SSIM-RE/MotionGame/firmware/MotionGame/menu_icons.cpp

#include"menu_icons.h"

const uint8_t ICON_GAME_64[512] = {
    0x00, 0x00, 0x00, 0x00, 0x00, 0x00, 0x00, 0x00, 0x00, 0x00, 0x00, 0x00,
    0x00, 0x00, 0x00, 0x00, 0x00, 0x00, 0x00, 0x00, 0x00, 0x00, 0x00, 0x00,
    0x00, 0x00, 0x00, 0x00, 0x00, 0x00, 0x00, 0x00, 0x00, 0x00, 0x00, 0x00,
    0x00, 0x00, 0x00, 0x00, 0x00, 0x00, 0x00, 0x00, 0x00, 0x00, 0x00, 0x00,
    0x00, 0x00, 0x00, 0x00, 0x00, 0x00, 0x00, 0x00, 0x00, 0x00, 0x00, 0x00,
    0x00, 0x00, 0x00, 0x00, 0x00, 0x00, 0x00, 0x00, 0x00, 0x00, 0x00, 0x00,
    0x00, 0x00, 0x00, 0x00, 0x00, 0x00, 0x00, 0x00, 0x00, 0x00, 0x00, 0x00,
    0x00, 0x00, 0x00, 0x00, 0x00, 0x00, 0x00, 0x00, 0x00, 0x00, 0x00, 0x00,
    0x00, 0x00, 0x00, 0x00, 0x00, 0x00, 0x00, 0x00, 0x00, 0x00, 0x00, 0x00,
    0x00, 0x00, 0x00, 0x00, 0x00, 0x00, 0x00, 0x00, 0x00, 0x00, 0x00, 0x00,
    0x00, 0x00, 0x68, 0x00, 0x00, 0x2D, 0x00, 0x00, 0x00, 0x03, 0xFF, 0x00,
    0x00, 0xFF, 0xC0, 0x00, 0x00, 0x0F, 0xD7, 0x80, 0x01, 0xD5, 0xE0, 0x00,
    0x00, 0x0E, 0x00, 0xFF, 0xFF, 0x00, 0x78, 0x00, 0x00, 0x1C, 0x00, 0x7F,
    0xFE, 0x00, 0x38, 0x00, 0x00, 0x38, 0x00, 0x00, 0x00, 0x04, 0x1C, 0x00,
    0x00, 0x30, 0x28, 0x00, 0x00, 0x1C, 0x0C, 0x00, 0x00, 0x30, 0x38, 0x00,
    0x00, 0x1E, 0x04, 0x00, 0x00, 0x60, 0x78, 0x1C, 0x38, 0x0C, 0x06, 0x00,
    0x00, 0x60, 0x38, 0x1E, 0x78, 0x00, 0x06, 0x00, 0x00, 0x63, 0xD7, 0x08,
    0x21, 0xE1, 0xE6, 0x00, 0x00, 0x43, 0xCF, 0x80, 0x01, 0xE1, 0xE2, 0x00,
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
    0xF0, 0x00, 0x0F, 0x00, 0x00, 0x78, 0x00, 0x0F, 0xF8, 0x00, 0x0F, 0x00,
    0x00, 0x78, 0x00, 0x7F, 0xFE, 0x00, 0x1E, 0x00, 0x00, 0x3C, 0x00, 0x7F,
    0xFE, 0x00, 0x3C, 0x00, 0x00, 0x1E, 0x00, 0x7F, 0xFE, 0x00, 0x3C, 0x00,
    0x00, 0x1F, 0x00, 0x00, 0x00, 0x00, 0xF8, 0x00, 0x00, 0x0F, 0x80, 0x00,
    0x00, 0x01, 0xF0, 0x00, 0x00, 0x07, 0xC0, 0x00, 0x00, 0x03, 0xE0, 0x00,
    0x00, 0x03, 0xF0, 0x00, 0x00, 0x07, 0xC0, 0x00, 0x00, 0x01, 0xF8, 0x00,
    0x00, 0x1F, 0x80, 0x00, 0x00, 0x00, 0x7E, 0x00, 0x00, 0x7F, 0x00, 0x00,
    0x00, 0x00, 0x3F, 0xC0, 0x03, 0xFC, 0x00, 0x00, 0x00, 0x00, 0x0F, 0xFF,
    0x7F, 0xF8, 0x00, 0x00, 0x00, 0x00, 0x03, 0xFF, 0xFF, 0xE0, 0x00, 0x00,
    0x00, 0x00, 0x00, 0xFF, 0xFF, 0x00, 0x00, 0x00, 0x00, 0x00, 0x00, 0x05,
    0xA0, 0x00, 0x00, 0x00, 0x00, 0x00, 0x00, 0x00, 0x00, 0x00, 0x00, 0x00,
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
};
