SSIM-RE/MotionGame/firmware/MotionGame/menu_icons.h

#pragma once
#include <stdint.h>
#define ICON_W 64
#define ICON_H 64
#define SCREEN_W 128
#define SCREEN_H 160
extern const uint8_t ICON_GAME_64[];
extern const uint8_t ICON_THEME_64[];
extern const uint8_t ICON_SETTINGS_64[];
extern const uint8_t ICON_ABOUT_64[];
